KozAAAAA/TemperatureManagementGUI/worker.cpp

#include "worker.h"

#define H 5 // adjust to change the behaviour of hysteresis

Worker::Worker(const std::vector<quint16>& m_tempInputVector_,
               const std::vector<quint16>& m_timeInputVector_,
               const quint8& m_loopInput_) :
    QThread(),

    m_tempInputVector(m_tempInputVector_),
    m_timeInputVector(m_timeInputVector_),
    m_loopInput(m_loopInput_),

    m_threadActive(true),

    m_currentTemp(0),
    m_currentTime(0),
    m_currentLoop(1),
    m_currentBlock(1),

    m_isRelayOn(true)

    {setRelayOff();}

Worker::~Worker()
{
    setRelayOff();
    qDebug()<<"WORKER - has been deleted";
}

    //------------------------------INPUT-----------------------------//
void Worker::setThreadNotActive()
{
    m_threadActive = false;
}
    //----------------------------------------------------------------//

    //-----------------------------METHODS----------------------------//
void Worker::run()
{
    qDebug()<<"START HAS BEEN PRESSED - thread is activated";

    for(;m_currentLoop < m_loopInput+1;m_currentLoop++)
    {
        emit currentLoop(m_currentLoop);
        for(;m_currentBlock < 5; m_currentBlock++)
        {
            //h to ms:
//            quint32 m_workingTimeMs = 36e5 * m_timeInputVector[m_currentBlock-1]/100;
            //fake time:
            quint32 m_workingTimeMs = 36e5 * m_timeInputVector[m_currentBlock-1]/3600/100;

            m_timer.start();

            if(m_workingTimeMs!=0)
            {
                emit currentBlock(m_currentBlock);

                while((!m_timer.hasExpired(m_workingTimeMs)) &&
                        m_threadActive)
                {
                    m_currentTime = (m_workingTimeMs - m_timer.elapsed());
                    emit currentTime(m_currentTime);

                    hysteresis();
                }
            }
        }
        m_currentBlock = 0;
    }
    m_currentLoop = 0;
    outputReset();

    qDebug()<<"STOP HAS BEEN PRESSED - thread is not active";
}
void Worker::hysteresis()
{
    try
    {
        m_currentTemp = getTempSensor();
    }

    catch (const char* msg)
    {
        setRelayOff();
        m_threadActive = false;
        qDebug() << msg;
        std::terminate();
    }

    emit currentTemp(m_currentTemp);
    if(m_currentTemp < m_tempInputVector[m_currentBlock-1] + (H/2))
    {
        setRelayOn();
    }
    if(m_currentTemp > m_tempInputVector[m_currentBlock-1] - (H/2))
    {
        setRelayOff();
    }

}

float Worker::getTempSensor()
{

    if (std::system("./MAX31865.py") != 0)
        throw "ERROR - python file not found";

    QFile file("tempSensor.txt");

    if (!file.open(QIODevice::ReadOnly | QIODevice::Text))
        throw "ERROR - .txt file not found";

    QTextStream in(&file);
    QString redTemp = in.readLine();
    return redTemp.toFloat();
}
void Worker::setRelayOn()
{
    if(m_isRelayOn == false)
    {
        #ifdef __arm__
            digitalWrite(0,HIGH);
        #endif

        m_isRelayOn = true;

        emit relayIsOn();

        qDebug()<<"heating is on";
    }
}
void Worker::setRelayOff()
{
    if(m_isRelayOn == true)
    {
        #ifdef __arm__
            digitalWrite(0,LOW);
        #endif

        m_isRelayOn = false;

        emit relayIsOff();

        qDebug()<<"heating is off";
    }
}
void Worker::outputReset()
{
    emit currentTemp(0);
    emit currentTime(0);
    emit currentLoop(0);
    emit currentBlock(0);
}

    //----------------------------------------------------------------//
